gbrickell/ESP32_maker_PCB/ESP32_code/motor_control/servo_motors/ESP32_PCA9686_btn_servo/ESP32_PCA9686_btn_servo.ino

/*************************************************** 
  Modified version of a test example for the ESP32 Maker Kit
  using the Adafruit 16-channel PWM & Servo driver with the 
  PCA9685 I2C PWM module - drives multiple servos one after 
  the other on the PCA9685 channels starting at channel 0
  but only when button 1 is pressed
 ****************************************************/

#include <Wire.h>
#include <Adafruit_PWMServoDriver.h>

// called this way, it uses the PCA9685 default I2C address 0x40
Adafruit_PWMServoDriver pwm = Adafruit_PWMServoDriver();
// you can also call it with a different address you want
//Adafruit_PWMServoDriver pwm = Adafruit_PWMServoDriver(0x41);
// you can also call it with a different address and I2C interface
//Adafruit_PWMServoDriver pwm = Adafruit_PWMServoDriver(0x40, Wire);

// Depending on the servo make, the pulse width min and max may vary, 
// need to be as small/large as possible without hitting the hard stop
// for max range. Tweak them as necessary to match the servos used
#define SERVOMIN  150 // This is the 'minimum' pulse length count (out of 4096)
#define SERVOMAX  600 // This is the 'maximum' pulse length count (out of 4096)
#define USMIN  600 // This is the rounded 'minimum' microsecond length based on the minimum pulse of 150
#define USMAX  2400 // This is the rounded 'maximum' microsecond length based on the maximum pulse of 600
#define SERVO_FREQ 50 // Analog servos run at ~50 Hz updates

uint8_t servonum = 0;  // this counter is incremented in the 'loop' cycle
int chanmax = 2;  // set this to the number of consecutive servo attached to the PCA9685

// button 2 used to trigger the servo test cycle
//  which is pulled-up with a physical resistor
int btn_pin = 34; // GPIO pin on one side of the bottom button (2)

void setup() {
  Serial.begin(115200);
  delay(1500); // short delay to set up the monitor
  Serial.println("program starting ..... ");
  
  // pins 1, 3, 5, 14, and 15 are set HIGH on boot - so set them LOW unless/until they are needed
  pinMode(1, OUTPUT);
  pinMode(3, OUTPUT);
  pinMode(5, OUTPUT);
  pinMode(14, OUTPUT);
  pinMode(15, OUTPUT);
  digitalWrite(1, LOW);
  digitalWrite(3, LOW);
  digitalWrite(5, LOW);
  digitalWrite(14, LOW);
  digitalWrite(15, LOW);

  pinMode(btn_pin, INPUT); // make the button connected GPIO pin an INPUT
  
  Serial.print(chanmax);
  Serial.println(" channel servo test!");
  Serial.println("press button 2 to start the test ..");
  Serial.println("... and press again to use the next servo ");

  pwm.begin();
  /*
   * In theory the internal oscillator (clock) is 25MHz but it really isn't
   * that precise. You can 'calibrate' this by tweaking this number until
   * you get the PWM update frequency you're expecting!
   * The int.osc. for the PCA9685 chip is a range between about 23-27MHz and
   * is used for calculating things like writeMicroseconds()
   * Analog servos run at ~50 Hz updates, It is importaint to use an
   * oscilloscope in setting the int.osc frequency for the I2C PCA9685 chip.
   * 1) Attach the oscilloscope to one of the PWM signal pins and ground on
   *    the I2C PCA9685 chip you are setting the value for.
   * 2) Adjust setOscillatorFrequency() until the PWM update frequency is the
   *    expected value (50Hz for most ESCs)
   * Setting the value here is specific to each individual I2C PCA9685 chip and
   * affects the calculations for the PWM update frequency. 
   * Failure to correctly set the int.osc value will cause unexpected PWM results
   */
  pwm.setOscillatorFrequency(27000000);
  pwm.setPWMFreq(SERVO_FREQ);  // Analog servos run at ~50 Hz updates

  delay(10);
}

// *************************************************************************
// You can use this function if you'd like to set the pulse length in seconds
// e.g. setServoPulse(0, 0.001) is a ~1 millisecond pulse width. It's not precise!
// *************************************************************************
void setServoPulse(uint8_t n, double pulse) {
  double pulselength;
  
  pulselength = 1000000;   // 1,000,000 us per second
  pulselength /= SERVO_FREQ;   // Analog servos run at ~60 Hz updates
  Serial.print(pulselength); Serial.println(" us per period"); 
  pulselength /= 4096;  // 12 bits of resolution
  Serial.print(pulselength); Serial.println(" us per bit"); 
  pulse *= 1000000;  // convert input seconds to us
  pulse /= pulselength;
  Serial.println(pulse);
  pwm.setPWM(n, 0, pulse);
}


void loop() {

  if (digitalRead(btn_pin) == LOW) {  // check if button has been pressed
    // if here button has been pressed so do the servo test cycle
    Serial.println("button pressed, starting servo test cycle ......");

    Serial.print("PCA9685 channel ");
    Serial.println(servonum);
    // Drive each servo one at a time using setPWM()
    for (uint16_t pulselen = SERVOMIN; pulselen < SERVOMAX; pulselen++) {
      pwm.setPWM(servonum, 0, pulselen);
    }

    delay(500);
    for (uint16_t pulselen = SERVOMAX; pulselen > SERVOMIN; pulselen--) {
      pwm.setPWM(servonum, 0, pulselen);
    }

    delay(500);

    // Drive each servo one at a time using writeMicroseconds(), it's not precise due to calculation rounding!
    // The writeMicroseconds() function is used to mimic the Arduino Servo library writeMicroseconds() behavior. 
    for (uint16_t microsec = USMIN; microsec < USMAX; microsec++) {
      pwm.writeMicroseconds(servonum, microsec);
    }

    delay(500);
    for (uint16_t microsec = USMAX; microsec > USMIN; microsec--) {
      pwm.writeMicroseconds(servonum, microsec);
    }

    delay(500);

    servonum++;
    if (servonum > chanmax-1) servonum = 0; // Testing 'chanmax' servo channels starting at 0

  }

}
