gbrickell/ESP32_maker_PCB/ESP32_code/displays/ESP32_IPS_240X240_SPI/240x240_ST7789_drawXBitmap/cat240x180.h

// Images can be converted to XBM format by using the online converter here:
// https://convertio.co/jpg-xbm/
// The output must be pasted in a header file, renamed and adjusted to appear
// as as a const unsigned char array in PROGMEM (FLASH program memory), i.e. like this file!

// The xbm format adds padding to pixel rows so they are a whole number of bytes

// The library ignores the padding bits when drawing the image on the display.

// Example of the correct format is shown below

// cat 240 x 180 pixel array in XBM format
#define catWidth  240  // cat width
#define catHeight 180   // cat height

// Image is stored in this array
PROGMEM const unsigned char cat[] = {
  0x00, 0x00, 0x00, 0x00, 0x00, 0x00, 0x00, 0x00, 0x00, 0x00, 0x62, 0x40, 
  0x08, 0x50, 0x00, 0x01, 0x00, 0x02, 0x00, 0x00, 0x00, 0x12, 0x10, 0x04, 
  0x09, 0x00, 0x00, 0x00, 0x00, 0x00, 0x00, 0x00, 0x00, 0x00, 0x00, 0x00, 
  0x00, 0x00, 0x00, 0x40, 0x08, 0x00, 0x00, 0x00, 0x00, 0x00, 0x40, 0x14, 
  0x00, 0x40, 0x00, 0x80, 0x56, 0x51, 0x05, 0x00, 0x00, 0x00, 0x00, 0x00, 
  0x00, 0x00, 0x00, 0x00, 0x00, 0x00, 0x00, 0x00, 0x00, 0x20, 0x01, 0x08, 
  0x40, 0x00, 0x00, 0x00, 0x00, 0x00, 0x40, 0x00, 0x40, 0x00, 0x04, 0x04, 
  0x1C, 0x00, 0x00, 0x00, 0x00, 0x00, 0x00, 0x00, 0x00, 0x00, 0x00, 0x00, 
  0x00, 0x00, 0x80, 0x00, 0x00, 0x00, 0x00, 0x00, 0x00, 0x00, 0x00, 0x00, 
  0x02, 0x00, 0x00, 0x9A, 0x61, 0x22, 0x00, 0x00, 0x00, 0x00, 0x00, 0x00, 
  0x00, 0x00, 0x00, 0x00, 0x00, 0x00, 0x00, 0x00, 0x08, 0x00, 0x00, 0x00, 
  0x40, 0x00, 0x00, 0x00, 0x00, 0x10, 0x00, 0x00, 0x00, 0x40, 0x8A, 0x89, 
  0x80, 0x00, 0x00, 0x00, 0x00, 0x00, 0x00, 0x00, 0x00, 0x00, 0x00, 0x00, 
  0x00, 0xD0, 0x00, 0x00, 0x00, 0x10, 0x00, 0x01, 0x00, 0x00, 0x00, 0x00, 
  0x00, 0x00, 0x00, 0x08, 0x22, 0x18, 0x15, 0x00, 0x00, 0x00, 0x00, 0x00, 
  0x00, 0x00, 0x00, 0x00, 0x00, 0x00, 0x00, 0x09, 0x00, 0x00, 0x20, 0x04, 
  0x00, 0x00, 0x00, 0x00, 0x00, 0x00, 0x80, 0x00, 0x00, 0x90, 0x18, 0x02, 
  0x04, 0x00, 0x00, 0x00, 0x00, 0x00, 0x00, 0x00, 0x00, 0x00, 0x00, 0x00, 
  0x20, 0x12, 0x08, 0x00, 0x00, 0x00, 0x00, 0x00, 0x00, 0x00, 0x00, 0x00, 
  0x00, 0x00, 0x00, 0x00, 0x00, 0xA0, 0x21, 0x00, 0x00, 0x00, 0x00, 0x00, 
  0x00, 0x00, 0x00, 0x00, 0x00, 0x80, 0xC2, 0x04, 0x00, 0x02, 0x80, 0x00, 
  0x08, 0x00, 0x00, 0x00, 0x00, 0x00, 0x00, 0x00, 0x00, 0x00, 0xA4, 0x10, 
  0x12, 0x02, 0x00, 0x00, 0x00, 0x08, 0x00, 0x00, 0x00, 0x00, 0x00, 0x24, 
  0x20, 0x80, 0x00, 0x00, 0x00, 0x01, 0x00, 0x04, 0x00, 0x00, 0x00, 0x00, 
  0x00, 0x00, 0x00, 0x28, 0x00, 0x41, 0x88, 0x04, 0x00, 0x00, 0x00, 0x00, 
  0x00, 0x00, 0x00, 0x00, 0xA0, 0x05, 0x00, 0x00, 0x04, 0x00, 0x00, 0x00, 
  0x09, 0x00, 0x00, 0x00, 0x00, 0x00, 0x00, 0x00, 0x00, 0x00, 0x40, 0x88, 
  0x2A, 0x02, 0x00, 0x00, 0x00, 0x50, 0x00, 0x00, 0x00, 0x00, 0x4C, 0x49, 
  0x08, 0x00, 0x00, 0x04, 0x00, 0x84, 0x80, 0x44, 0x00, 0x00, 0x00, 0x00, 
  0x00, 0x00, 0x00, 0x00, 0x00, 0x00, 0x40, 0x10, 0x00, 0x00, 0x00, 0x00, 
  0x00, 0x00, 0x00, 0x40, 0x92, 0x00, 0x20, 0x00, 0x00, 0x00, 0x00, 0x04, 
  0x04, 0x05, 0x00, 0x00, 0x00, 0x00, 0x00, 0x00, 0x00, 0x00, 0x00, 0x08, 
  0x22, 0x10, 0x00, 0x00, 0x00, 0x48, 0x00, 0x00, 0x00, 0x48, 0x09, 0x00, 
  0x00, 0x00, 0x02, 0x00, 0x80, 0x00, 0x62, 0x02, 0x00, 0x00, 0x00, 0x00, 
  0x00, 0x00, 0x00, 0x00, 0x00, 0x00, 0x48, 0x08, 0x00, 0x00, 0x00, 0xA5, 
  0x00, 0x00, 0xA0, 0x21, 0x04, 0x08, 0x00, 0x00, 0x00, 0x00, 0x10, 0x04, 
  0xD4, 0x35, 0x02, 0x00, 0x00, 0x00, 0x00, 0x00, 0x00, 0x00, 0x00, 0x00, 
  0x02, 0x01, 0x00, 0x00, 0x00, 0xDB, 0x00, 0x00, 0xD5, 0x44, 0x00, 0x10, 
  0x00, 0x08, 0x00, 0x00, 0x60, 0x03, 0x28, 0x80, 0x00, 0x00, 0x00, 0x00, 
  0x00, 0x00, 0x00, 0x00, 0x00, 0x00, 0x20, 0x00, 0x00, 0x00, 0xE0, 0x14, 
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
  };
