gbrickell/ESP32_maker_PCB/ESP32_code/displays/ESP32_IPS_80x160_SPI/80x160_ST7735_drawXBitmap/cat107x80.h

// Images can be converted to XBM format by using the online converter here:
// https://convertio.co/jpg-xbm/
// The output must be pasted in a header file, renamed and adjusted to appear
// as as a const unsigned char array in PROGMEM (FLASH program memory), i.e. like this file!

// The xbm format adds padding to pixel rows so they are a whole number of bytes

// The library ignores the padding bits when drawing the image on the display.

// Example of the correct format is shown below

// cat 107 x 80 pixel array in XBM format
#define catWidth  107  // cat width
#define catHeight 80   // cat height

// Image is stored in this array
PROGMEM const unsigned char cat[] = {
  0x00, 0x00, 0x00, 0x00, 0x80, 0x40, 0x00, 0x00, 0x00, 0xC0, 0x50, 0x00, 
  0x00, 0x00, 0x00, 0x00, 0x00, 0x00, 0x00, 0x00, 0x00, 0x00, 0x00, 0x00, 
  0x4A, 0x00, 0x00, 0x00, 0x00, 0x00, 0x00, 0x10, 0x00, 0x02, 0x00, 0x00, 
  0x00, 0x10, 0x04, 0x00, 0x00, 0x00, 0x00, 0x00, 0x00, 0x01, 0x00, 0x00, 
  0x00, 0x00, 0x00, 0x00, 0x40, 0x00, 0x00, 0x00, 0x00, 0x00, 0x0A, 0x00, 
  0x00, 0x04, 0x00, 0x00, 0x00, 0x00, 0x92, 0x00, 0x00, 0x00, 0x00, 0x00, 
  0x02, 0x00, 0x00, 0x40, 0x00, 0x00, 0x00, 0x00, 0x00, 0x04, 0x00, 0x02, 
  0x00, 0x24, 0x00, 0x00, 0x40, 0x50, 0x05, 0x00, 0x00, 0x00, 0x80, 0x00, 
  0x80, 0x01, 0x00, 0x08, 0x00, 0x00, 0x80, 0x22, 0x00, 0x00, 0x00, 0x00, 
  0x00, 0x00, 0x00, 0x01, 0x2D, 0x0A, 0x00, 0x00, 0x40, 0x94, 0x05, 0x00, 
  0x00, 0x00, 0x00, 0x00, 0x00, 0x00, 0x00, 0x00, 0x00, 0x00, 0xA8, 0x69, 
  0xC0, 0x01, 0x00, 0x00, 0x00, 0x00, 0x08, 0x04, 0x10, 0x00, 0x00, 0x00, 
  0x46, 0x02, 0x81, 0x02, 0x00, 0x00, 0x00, 0x00, 0x00, 0x00, 0x01, 0x00, 
  0x00, 0x00, 0x1B, 0x98, 0xF6, 0x01, 0x00, 0x00, 0x00, 0x00, 0x80, 0x00, 
  0x09, 0x00, 0x00, 0xC0, 0x04, 0x50, 0x2D, 0x01, 0x00, 0x00, 0x00, 0x00, 
  0x00, 0x00, 0x1F, 0x00, 0x00, 0x40, 0x61, 0xA7, 0xFA, 0x07, 0x00, 0x00, 
  0x00, 0x00, 0x00, 0x01, 0xDF, 0x00, 0x00, 0xA0, 0xB0, 0x5A, 0xFF, 0x01, 
  0x00, 0x00, 0x00, 0x00, 0x00, 0x00, 0xFF, 0x01, 0x00, 0x60, 0x66, 0xF5, 
  0xFD, 0x07, 0x00, 0x00, 0x00, 0x00, 0x40, 0x00, 0xFF, 0x1F, 0x00, 0x90, 
  0x7B, 0xE6, 0xDD, 0x2F, 0x00, 0x00, 0x00, 0x00, 0x00, 0x00, 0xFF, 0x3F, 
  0x00, 0x71, 0x0C, 0xFD, 0x7F, 0x1B, 0x00, 0x00, 0x00, 0x00, 0x00, 0x00, 
  0xFB, 0xFF, 0x80, 0x7E, 0x94, 0xFD, 0xDD, 0xFF, 0x00, 0x00, 0x00, 0x00, 
  0x00, 0x00, 0xFF, 0xFF, 0xF2, 0xDF, 0xEB, 0xAF, 0xD7, 0xBE, 0x01, 0x00, 
  0x00, 0x00, 0x00, 0x00, 0xFF, 0xFF, 0xFB, 0xFE, 0xEB, 0xBD, 0x7A, 0xBF, 
  0x05, 0x00, 0x00, 0x00, 0x00, 0x00, 0xFA, 0xFF, 0xFF, 0xF7, 0x85, 0xFF, 
  0xFF, 0xFF, 0x0B, 0x00, 0x00, 0x00, 0x00, 0x00, 0xFF, 0xFF, 0xFB, 0xF9, 
  0xFF, 0x7D, 0xBF, 0xFF, 0x0F, 0x00, 0x00, 0x00, 0x00, 0x00, 0xFE, 0xFF, 
  0xBF, 0xF6, 0x27, 0xFF, 0xF7, 0xFF, 0x7B, 0x00, 0x00, 0x00, 0x00, 0x00, 
  0xED, 0xFF, 0xFF, 0xFB, 0x3F, 0xFE, 0xFF, 0xFF, 0x9F, 0x00, 0x00, 0x00, 
  0x00, 0x00, 0xFB, 0xFF, 0xFF, 0xFF, 0xBF, 0xFF, 0xFF, 0xFF, 0xFE, 0x01, 
  0x00, 0x00, 0x00, 0x00, 0xEF, 0xBF, 0xFF, 0xFF, 0x5F, 0x3E, 0xFF, 0xBF, 
  0xFF, 0x07, 0x00, 0x00, 0x00, 0x00, 0xFA, 0xFF, 0x7F, 0xFE, 0xFF, 0xFB, 
  0xFF, 0xCF, 0x7B, 0x05, 0x00, 0x00, 0x00, 0x00, 0xFB, 0xBF, 0xFF, 0xFF, 
  0xFF, 0xFF, 0xFF, 0xE7, 0xFF, 0x1F, 0x00, 0x00, 0x00, 0x00, 0xBE, 0xFF, 
  0xEF, 0xFD, 0x7F, 0xFF, 0xFF, 0xFB, 0xFF, 0x77, 0x00, 0x00, 0x00, 0x00, 
  0xED, 0xBF, 0xFC, 0xFF, 0xFF, 0xFF, 0xEF, 0xF4, 0xFF, 0xFF, 0x3D, 0x00, 
  0x02, 0x00, 0xFF, 0xBF, 0xBF, 0xFD, 0xBF, 0xFF, 0xFF, 0xFE, 0x7F, 0xE5, 
  0xB7, 0xC0, 0x01, 0x00, 0xFE, 0xBF, 0xFE, 0xFD, 0xFF, 0xFF, 0xBB, 0xFE, 
  0xFF, 0xFF, 0xFF, 0xFF, 0x00, 0x00, 0xBA, 0x2E, 0xDD, 0xFF, 0xFF, 0xFF, 
  0x7F, 0xFE, 0xFF, 0xFF, 0xFF, 0xFF, 0x00, 0x00, 0xFF, 0x9F, 0xFF, 0xFE, 
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
