gbrickell/ESP32_maker_PCB/ESP32_code/displays/ESP32_IPS_80x160_SPI/80x160_ST7735_drawXBitmap/star80x80.h

// Images can be converted to XBM format by using the online converter here:
// https://convertio.co/jpg-xbm/
// The output must be pasted in a header file, renamed and adjusted to appear
// as as a const unsigned char array in PROGMEM (FLASH program memory), i.e. like this file!

// The xbm format adds padding to pixel rows so they are a whole number of bytes

// The library ignores the padding bits when drawing the image on the display.

// Example of the correct format is shown below

// star logo 80 x 80 pixel array in XBM format
#define starWidth  80  // star width
#define starHeight 80  // star height

// Image is stored in this array
PROGMEM const unsigned char star[] = {
  0xFF, 0xFF, 0xFF, 0xFF, 0xFF, 0xFF, 0xFF, 0xFF, 0xFF, 0xFF, 0xFF, 0xFF, 
  0xFF, 0xFF, 0xFF, 0xFF, 0xFF, 0xFF, 0xFF, 0xFF, 0xFF, 0xFF, 0xFF, 0xFF, 
  0xFF, 0xFF, 0xFF, 0xFF, 0xFF, 0xFF, 0xFF, 0xFF, 0xFF, 0xFF, 0xFF, 0xFF, 
  0xFF, 0xFF, 0xFF, 0xFF, 0xFF, 0xFF, 0xFF, 0xFF, 0xFF, 0xFF, 0xFF, 0xFF, 
  0xFF, 0xFF, 0xFF, 0xFF, 0xFF, 0xFF, 0xFF, 0xFE, 0xFF, 0xFF, 0xFF, 0xFF, 
  0xFF, 0xFF, 0xFF, 0xFF, 0x7F, 0xFE, 0xFF, 0xFF, 0xFF, 0xFF, 0xFF, 0xFF, 
  0xFF, 0xFF, 0xBF, 0xFE, 0xFF, 0xFF, 0xFF, 0xFF, 0xFF, 0xFF, 0xFF, 0xFF, 
  0xBF, 0xFC, 0xFF, 0xFF, 0xFF, 0xFF, 0xFF, 0xFF, 0xFF, 0xFF, 0x5F, 0xF6, 
  0xFF, 0xFF, 0xFF, 0xFF, 0xFF, 0xFF, 0xFF, 0xFF, 0x5F, 0xF8, 0xFF, 0xFF, 
  0xFF, 0xFF, 0xFF, 0xFF, 0xFF, 0xFF, 0x2F, 0xF5, 0xFF, 0xFF, 0xFF, 0xFF, 
  0xFF, 0xFF, 0xFF, 0xFF, 0xA7, 0xF4, 0xFF, 0xFF, 0xFF, 0xFF, 0xFF, 0xFF, 
  0xFF, 0xFF, 0x1F, 0xC1, 0xFF, 0xFF, 0xFF, 0xFF, 0xFF, 0xFF, 0xFF, 0xFF, 
  0xA3, 0xDA, 0xFF, 0xFF, 0xFF, 0xFF, 0xFF, 0xFF, 0xFF, 0xFF, 0x07, 0xA0, 
  0xFF, 0xFF, 0xFF, 0xFF, 0xFF, 0xFF, 0xFF, 0xFF, 0x2B, 0xA4, 0xFF, 0xFF, 
  0xFF, 0xFF, 0xFF, 0xFF, 0xFF, 0xFF, 0x84, 0x40, 0xFF, 0xFF, 0xFF, 0xFF, 
  0xFF, 0xFB, 0xFF, 0x7F, 0x02, 0x68, 0xFE, 0xFF, 0xDF, 0xFF, 0xFF, 0x5F, 
  0xF5, 0xFF, 0x25, 0x80, 0xFF, 0xBF, 0xEA, 0xFF, 0xFF, 0xA7, 0xBA, 0x7D, 
  0x02, 0x10, 0x7C, 0x46, 0xF3, 0xFF, 0xFF, 0x5F, 0x44, 0xAA, 0x04, 0x88, 
  0x8A, 0x69, 0xE8, 0xFF, 0xFF, 0x0F, 0x15, 0x65, 0x00, 0x00, 0x3A, 0x14, 
  0xF9, 0xFF, 0xFF, 0x6F, 0x40, 0x08, 0x02, 0x90, 0x81, 0x81, 0xF4, 0xFF, 
  0xFF, 0x5F, 0x29, 0xA5, 0x01, 0x00, 0x11, 0x44, 0xF4, 0xFF, 0xFF, 0xBF, 
  0x00, 0x00, 0x00, 0x00, 0x04, 0x40, 0xF9, 0xFF, 0xFF, 0x9F, 0x01, 0x01, 
  0x00, 0x00, 0x08, 0x01, 0xFE, 0xFF, 0xFF, 0x7F, 0x24, 0x00, 0x02, 0x00, 
  0x00, 0x40, 0xF9, 0xFF, 0xFF, 0xBF, 0x09, 0x00, 0x00, 0x00, 0x00, 0x40, 
  0xFD, 0xFF, 0xFF, 0x7F, 0x09, 0x00, 0x00, 0x00, 0x00, 0x90, 0xFC, 0xFF, 
  0xFF, 0x7F, 0x04, 0x00, 0x00, 0x00, 0x00, 0x80, 0xFE, 0xFF, 0xFF, 0xFF, 
  0x11, 0x00, 0x00, 0x00, 0x00, 0x44, 0xFF, 0xFF, 0xFF, 0xFF, 0x14, 0x00, 
  0x00, 0x00, 0x00, 0x88, 0xFE, 0xFF, 0xFF, 0xFF, 0x83, 0x00, 0x00, 0x00, 
  0x00, 0x60, 0xFF, 0xFF, 0xFF, 0xFF, 0x2A, 0x00, 0x00, 0x00, 0x00, 0x90, 
  0xFF, 0xFF, 0xFF, 0xFF, 0x09, 0x00, 0x00, 0x00, 0x00, 0x48, 0xFF, 0xFF, 
  0xFF, 0xFF, 0x4B, 0x00, 0x00, 0x00, 0x00, 0xA0, 0xFF, 0xFF, 0xFF, 0xFF, 
  0x15, 0x00, 0x00, 0x00, 0x00, 0x5C, 0xFF, 0xFF, 0xFF, 0xFF, 0x02, 0x00, 
  0x00, 0x00, 0x00, 0x80, 0xFE, 0xFF, 0xFF, 0x7F, 0x15, 0x00, 0x00, 0x00, 
  0x00, 0x31, 0xFE, 0xFF, 0xFF, 0xBF, 0x20, 0x00, 0x00, 0x00, 0x00, 0x80, 
  0xFA, 0xFF, 0xFF, 0x5F, 0x06, 0x00, 0x00, 0x00, 0x00, 0x20, 0xF6, 0xFF, 
  0xFF, 0x2F, 0x02, 0x00, 0x00, 0x00, 0x00, 0x40, 0xF5, 0xFF, 0xFF, 0x93, 
  0x00, 0x00, 0x00, 0x00, 0x00, 0x10, 0xC8, 0xFF, 0xFF, 0x5B, 0x00, 0x00, 
  0x00, 0x00, 0x00, 0x00, 0xD1, 0xFF, 0xFF, 0x06, 0x00, 0x00, 0x00, 0x00, 
  0x00, 0x00, 0x24, 0xFF, 0xFF, 0x29, 0x00, 0x00, 0x00, 0x00, 0x00, 0x00, 
  0x44, 0xFE, 0x7F, 0x42, 0x00, 0x00, 0x00, 0x00, 0x00, 0x40, 0x90, 0xFE, 
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
