gbrickell/ESP32_maker_PCB/ESP32_code/SD_card/SD_reader_OLED_SPI_test01/Open_Sans_Regular_12.h

// changed the character type below from const char to const uint8_t to correct compilation error
const uint8_t Open_Sans_Regular_12[] PROGMEM = {
	0x0B, // Width: 11
	0x11, // Height: 17
	0x20, // First Char: 32
	0xE0, // Numbers of Chars: 224

	// Jump Table:
	0xFF, 0xFF, 0x00, 0x03,  // 32:65535
	0x00, 0x00, 0x05, 0x03,  // 33:0
	0x00, 0x05, 0x0A, 0x05,  // 34:5
	0x00, 0x0F, 0x16, 0x08,  // 35:15
	0x00, 0x25, 0x11, 0x07,  // 36:37
	0x00, 0x36, 0x1A, 0x0A,  // 37:54
	0x00, 0x50, 0x17, 0x09,  // 38:80
	0x00, 0x67, 0x04, 0x03,  // 39:103
	0x00, 0x6B, 0x08, 0x04,  // 40:107
	0x00, 0x73, 0x08, 0x04,  // 41:115
	0x00, 0x7B, 0x11, 0x07,  // 42:123
	0x00, 0x8C, 0x11, 0x07,  // 43:140
	0x00, 0x9D, 0x05, 0x03,  // 44:157
	0x00, 0xA2, 0x08, 0x04,  // 45:162
	0x00, 0xAA, 0x05, 0x03,  // 46:170
	0x00, 0xAF, 0x0A, 0x04,  // 47:175
	0x00, 0xB9, 0x11, 0x07,  // 48:185
	0x00, 0xCA, 0x0B, 0x07,  // 49:202
	0x00, 0xD5, 0x11, 0x07,  // 50:213
	0x00, 0xE6, 0x11, 0x07,  // 51:230
	0x00, 0xF7, 0x14, 0x07,  // 52:247
	0x01, 0x0B, 0x11, 0x07,  // 53:267
	0x01, 0x1C, 0x11, 0x07,  // 54:284
	0x01, 0x2D, 0x10, 0x07,  // 55:301
	0x01, 0x3D, 0x11, 0x07,  // 56:317
	0x01, 0x4E, 0x11, 0x07,  // 57:334
	0x01, 0x5F, 0x05, 0x03,  // 58:351
	0x01, 0x64, 0x05, 0x03,  // 59:356
	0x01, 0x69, 0x11, 0x07,  // 60:361
	0x01, 0x7A, 0x11, 0x07,  // 61:378
	0x01, 0x8B, 0x11, 0x07,  // 62:395
	0x01, 0x9C, 0x0D, 0x05,  // 63:412
	0x01, 0xA9, 0x1D, 0x0B,  // 64:425
	0x01, 0xC6, 0x17, 0x08,  // 65:454
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
	0x00,0x00,0x00,0xF0,0x1F,0x00,0x10,0x11,0x00,0x10,0x11,0x00,0x10,0x11,0x00,0x10,0x11,0x00,0xE0,0x0E,	// 66
	0x00,0x00,0x00,0xC0,0x07,0x00,0x20,0x08,0x00,0x10,0x10,0x00,0x10,0x10,0x00,0x10,0x10,0x00,0x10,0x10,0x00,0x10,	// 67
	0x00,0x00,0x00,0xF0,0x1F,0x00,0x10,0x10,0x00,0x10,0x10,0x00,0x10,0x10,0x00,0x10,0x10,0x00,0x20,0x08,0x00,0xC0,0x07,	// 68
	0x00,0x00,0x00,0xF0,0x1F,0x00,0x10,0x11,0x00,0x10,0x11,0x00,0x10,0x11,0x00,0x10,0x11,	// 69
	0x00,0x00,0x00,0xF0,0x1F,0x00,0x10,0x01,0x00,0x10,0x01,0x00,0x10,0x01,0x00,0x10,0x01,	// 70
	0x00,0x00,0x00,0xC0,0x07,0x00,0x20,0x08,0x00,0x10,0x10,0x00,0x10,0x10,0x00,0x10,0x11,0x00,0x10,0x11,0x00,0x10,0x1F,	// 71
	0x00,0x00,0x00,0xF0,0x1F,0x00,0x00,0x01,0x00,0x00,0x01,0x00,0x00,0x01,0x00,0x00,0x01,0x00,0x00,0x01,0x00,0xF0,0x1F,	// 72
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
};
