gbrickell/ESP32_maker_PCB/ESP32_code/SD_card/SD_reader_OLED_SPI_test01/Open_Sans_Regular_16.h

// changed the character type below from const char to const uint8_t to correct compilation error
const uint8_t Open_Sans_Regular_16[] PROGMEM = {
	0x0F, // Width: 15
	0x17, // Height: 23
	0x20, // First Char: 32
	0xE0, // Numbers of Chars: 224

	// Jump Table:
	0xFF, 0xFF, 0x00, 0x04,  // 32:65535
	0x00, 0x00, 0x09, 0x04,  // 33:0
	0x00, 0x09, 0x0E, 0x06,  // 34:9
	0x00, 0x17, 0x1D, 0x0A,  // 35:23
	0x00, 0x34, 0x17, 0x09,  // 36:52
	0x00, 0x4B, 0x24, 0x0D,  // 37:75
	0x00, 0x6F, 0x21, 0x0C,  // 38:111
	0x00, 0x90, 0x07, 0x04,  // 39:144
	0x00, 0x97, 0x0C, 0x05,  // 40:151
	0x00, 0xA3, 0x0C, 0x05,  // 41:163
	0x00, 0xAF, 0x17, 0x09,  // 42:175
	0x00, 0xC6, 0x17, 0x09,  // 43:198
	0x00, 0xDD, 0x09, 0x04,  // 44:221
	0x00, 0xE6, 0x0B, 0x05,  // 45:230
	0x00, 0xF1, 0x09, 0x04,  // 46:241
	0x00, 0xFA, 0x10, 0x06,  // 47:250
	0x01, 0x0A, 0x17, 0x09,  // 48:266
	0x01, 0x21, 0x12, 0x09,  // 49:289
	0x01, 0x33, 0x18, 0x09,  // 50:307
	0x01, 0x4B, 0x17, 0x09,  // 51:331
	0x01, 0x62, 0x1A, 0x09,  // 52:354
	0x01, 0x7C, 0x17, 0x09,  // 53:380
	0x01, 0x93, 0x18, 0x09,  // 54:403
	0x01, 0xAB, 0x17, 0x09,  // 55:427
	0x01, 0xC2, 0x18, 0x09,  // 56:450
	0x01, 0xDA, 0x17, 0x09,  // 57:474
	0x01, 0xF1, 0x09, 0x04,  // 58:497
	0x01, 0xFA, 0x09, 0x04,  // 59:506
	0x02, 0x03, 0x17, 0x09,  // 60:515
	0x02, 0x1A, 0x17, 0x09,  // 61:538
	0x02, 0x31, 0x17, 0x09,  // 62:561
	0x02, 0x48, 0x14, 0x07,  // 63:584
	0x02, 0x5C, 0x26, 0x0E,  // 64:604
	0x02, 0x82, 0x1E, 0x0A,  // 65:642
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
	0x00,0x00,0x00,0x00,0x00,0x00,0xC0,0xFF,0x03,0x00,0x08,0x00,0x00,0x08,0x00,0x00,0x08,0x00,0x00,0x08,0x00,0x00,0x08,0x00,0x00,0x08,0x00,0xC0,0xFF,0x03,	// 72
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
};
