gbrickell/ESP32_maker_PCB/ESP32_code/SD_card/SD_reader_OLED_SPI_test01/Open_Sans_Regular_18.h

// changed the character type below from const char to const uint8_t to correct compilation error
const uint8_t Open_Sans_Regular_18[] PROGMEM = {
	0x11, // Width: 17
	0x1A, // Height: 26
	0x20, // First Char: 32
	0xE0, // Numbers of Chars: 224

	// Jump Table:
	0xFF, 0xFF, 0x00, 0x05,  // 32:65535
	0x00, 0x00, 0x0B, 0x05,  // 33:0
	0x00, 0x0B, 0x16, 0x07,  // 34:11
	0x00, 0x21, 0x2A, 0x0C,  // 35:33
	0x00, 0x4B, 0x23, 0x0A,  // 36:75
	0x00, 0x6E, 0x37, 0x0F,  // 37:110
	0x00, 0xA5, 0x2F, 0x0D,  // 38:165
	0x00, 0xD4, 0x0A, 0x04,  // 39:212
	0x00, 0xDE, 0x0F, 0x05,  // 40:222
	0x00, 0xED, 0x0F, 0x05,  // 41:237
	0x00, 0xFC, 0x22, 0x0A,  // 42:252
	0x01, 0x1E, 0x22, 0x0A,  // 43:286
	0x01, 0x40, 0x0B, 0x04,  // 44:320
	0x01, 0x4B, 0x12, 0x06,  // 45:331
	0x01, 0x5D, 0x0B, 0x05,  // 46:349
	0x01, 0x68, 0x19, 0x07,  // 47:360
	0x01, 0x81, 0x23, 0x0A,  // 48:385
	0x01, 0xA4, 0x17, 0x0A,  // 49:420
	0x01, 0xBB, 0x23, 0x0A,  // 50:443
	0x01, 0xDE, 0x23, 0x0A,  // 51:478
	0x02, 0x01, 0x27, 0x0A,  // 52:513
	0x02, 0x28, 0x23, 0x0A,  // 53:552
	0x02, 0x4B, 0x23, 0x0A,  // 54:587
	0x02, 0x6E, 0x22, 0x0A,  // 55:622
	0x02, 0x90, 0x23, 0x0A,  // 56:656
	0x02, 0xB3, 0x23, 0x0A,  // 57:691
	0x02, 0xD6, 0x0B, 0x05,  // 58:726
	0x02, 0xE1, 0x0B, 0x05,  // 59:737
	0x02, 0xEC, 0x23, 0x0A,  // 60:748
	0x03, 0x0F, 0x22, 0x0A,  // 61:783
	0x03, 0x31, 0x22, 0x0A,  // 62:817
	0x03, 0x53, 0x1A, 0x08,  // 63:851
	0x03, 0x6D, 0x3A, 0x10,  // 64:877
	0x03, 0xA7, 0x2B, 0x0B,  // 65:935
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
	0x00,0x00,0x00,0x00,0x00,0x00,0x00,0x00,0x80,0xFF,0x0F,0x00,0x80,0x00,0x08,0x00,0x80,0x00,0x08,0x00,0x80,0x00,0x08,0x00,0x80,0x00,0x08,0x00,0x80,0x00,0x08,0x00,0x00,0x01,0x04,0x00,0x00,0x03,0x06,0x00,0x00,0xFE,0x03,0x00,0x00,0xF8,	// 68
	0x00,0x00,0x00,0x00,0x00,0x00,0x00,0x00,0x80,0xFF,0x0F,0x00,0x80,0x20,0x08,0x00,0x80,0x20,0x08,0x00,0x80,0x20,0x08,0x00,0x80,0x20,0x08,0x00,0x80,0x20,0x08,0x00,0x80,0x20,0x08,	// 69
	0x00,0x00,0x00,0x00,0x00,0x00,0x00,0x00,0x80,0xFF,0x0F,0x00,0x80,0x20,0x00,0x00,0x80,0x20,0x00,0x00,0x80,0x20,0x00,0x00,0x80,0x20,0x00,0x00,0x80,0x20,0x00,0x00,0x80,	// 70
	0x00,0x00,0x00,0x00,0x00,0xF8,0x00,0x00,0x00,0xFE,0x03,0x00,0x00,0x03,0x06,0x00,0x00,0x01,0x0C,0x00,0x80,0x00,0x08,0x00,0x80,0x00,0x08,0x00,0x80,0x20,0x08,0x00,0x80,0x20,0x08,0x00,0x80,0x20,0x08,0x00,0x80,0xE1,0x0F,0x00,0x00,0xE0,0x07,	// 71
	0x00,0x00,0x00,0x00,0x00,0x00,0x00,0x00,0x80,0xFF,0x0F,0x00,0x00,0x20,0x00,0x00,0x00,0x20,0x00,0x00,0x00,0x20,0x00,0x00,0x00,0x20,0x00,0x00,0x00,0x20,0x00,0x00,0x00,0x20,0x00,0x00,0x00,0x20,0x00,0x00,0x80,0xFF,0x0F,	// 72
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
};
