gbrickell/ESP32_maker_PCB/ESP32_code/SD_card/SD_reader_OLED_SPI_test01/Open_Sans_Regular_24.h

// changed the character type below from const char to const uint8_t to correct compilation error
const uint8_t Open_Sans_Regular_24[] PROGMEM = {
	0x16, // Width: 22
	0x21, // Height: 33
	0x20, // First Char: 32
	0xE0, // Numbers of Chars: 224

	// Jump Table:
	0xFF, 0xFF, 0x00, 0x06,  // 32:65535
	0x00, 0x00, 0x18, 0x06,  // 33:0
	0x00, 0x18, 0x25, 0x0A,  // 34:24
	0x00, 0x3D, 0x48, 0x10,  // 35:61
	0x00, 0x85, 0x3A, 0x0E,  // 36:133
	0x00, 0xBF, 0x5D, 0x14,  // 37:191
	0x01, 0x1C, 0x54, 0x12,  // 38:284
	0x01, 0x70, 0x11, 0x05,  // 39:368
	0x01, 0x81, 0x1D, 0x07,  // 40:385
	0x01, 0x9E, 0x1C, 0x07,  // 41:414
	0x01, 0xBA, 0x39, 0x0D,  // 42:442
	0x01, 0xF3, 0x3F, 0x0E,  // 43:499
	0x02, 0x32, 0x13, 0x06,  // 44:562
	0x02, 0x45, 0x21, 0x08,  // 45:581
	0x02, 0x66, 0x18, 0x06,  // 46:614
	0x02, 0x7E, 0x2A, 0x09,  // 47:638
	0x02, 0xA8, 0x3F, 0x0E,  // 48:680
	0x02, 0xE7, 0x2C, 0x0E,  // 49:743
	0x03, 0x13, 0x40, 0x0E,  // 50:787
	0x03, 0x53, 0x3F, 0x0E,  // 51:851
	0x03, 0x92, 0x44, 0x0E,  // 52:914
	0x03, 0xD6, 0x3F, 0x0E,  // 53:982
	0x04, 0x15, 0x3F, 0x0E,  // 54:1045
	0x04, 0x54, 0x3E, 0x0E,  // 55:1108
	0x04, 0x92, 0x3F, 0x0E,  // 56:1170
	0x04, 0xD1, 0x3F, 0x0E,  // 57:1233
	0x05, 0x10, 0x18, 0x06,  // 58:1296
	0x05, 0x28, 0x13, 0x06,  // 59:1320
	0x05, 0x3B, 0x3F, 0x0E,  // 60:1339
	0x05, 0x7A, 0x3F, 0x0E,  // 61:1402
	0x05, 0xB9, 0x3F, 0x0E,  // 62:1465
	0x05, 0xF8, 0x2A, 0x0A,  // 63:1528
	0x06, 0x22, 0x67, 0x16,  // 64:1570
	0x06, 0x89, 0x4A, 0x0F,  // 65:1673
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
};
